gratinDeTopinambour/Moisture-sensor/Program/STM32U073CB/Drivers/CAPACITIVE_READING/Inc/capacitive_sensor.h

/*
 * capacitive_sensor.h
 *
 *  Created on: 31 juil. 2026
 *      Author: valentin
 */

#ifndef CAPACITIVE_READING_INC_CAPACITIVE_SENSOR_H_
#define CAPACITIVE_READING_INC_CAPACITIVE_SENSOR_H_

#include "main.h"

uint32_t read_capa_value(TSC_HandleTypeDef *htsc);


#endif /* CAPACITIVE_READING_INC_CAPACITIVE_SENSOR_H_ */
