gratinDeTopinambour/Moisture-sensor/Program/STM32U073CB/Drivers/LCD_3DIGIT/Inc/7segment_font.h

/*
 * 7segment_font.h
 *
 *  Created on: 31 juil. 2026
 *      Author: valentin
 */

#ifndef LCD_3DIGIT_INC_7SEGMENT_FONT_H_
#define LCD_3DIGIT_INC_7SEGMENT_FONT_H_

#include <stdint.h>

extern const uint8_t font7seg[];

#endif /* LCD_3DIGIT_INC_7SEGMENT_FONT_H_ */
